CMU-Robotics-Club/rtk-datalogger/scripts/utils.py

from tqdm import tqdm

# https://github.com/tqdm/tqdm/blob/0bb91857eca0d4aea08f66cf1c8949abe0cd6b7a/examples/tqdm_wget.py#L1
class TqdmUpTo(tqdm):
    """Alternative Class-based version of the above.
    Provides `update_to(n)` which uses `tqdm.update(delta_n)`.
    Inspired by [twine#242](https://github.com/pypa/twine/pull/242),
    [here](https://github.com/pypa/twine/commit/42e55e06).
    """

    def update_to(self, b=1, bsize=1, tsize=None):
        """
        b  : int, optional
            Number of blocks transferred so far [default: 1].
        bsize  : int, optional
            Size of each block (in tqdm units) [default: 1].
        tsize  : int, optional
            Total size (in tqdm units). If [default: None] remains unchanged.
        """
        if tsize is not None:
            self.total = tsize
        return self.update(b * bsize - self.n)  # also sets self.n = b * bsize
